cryptable/raspberry-sx/docs/images/IMG_2757.jpg

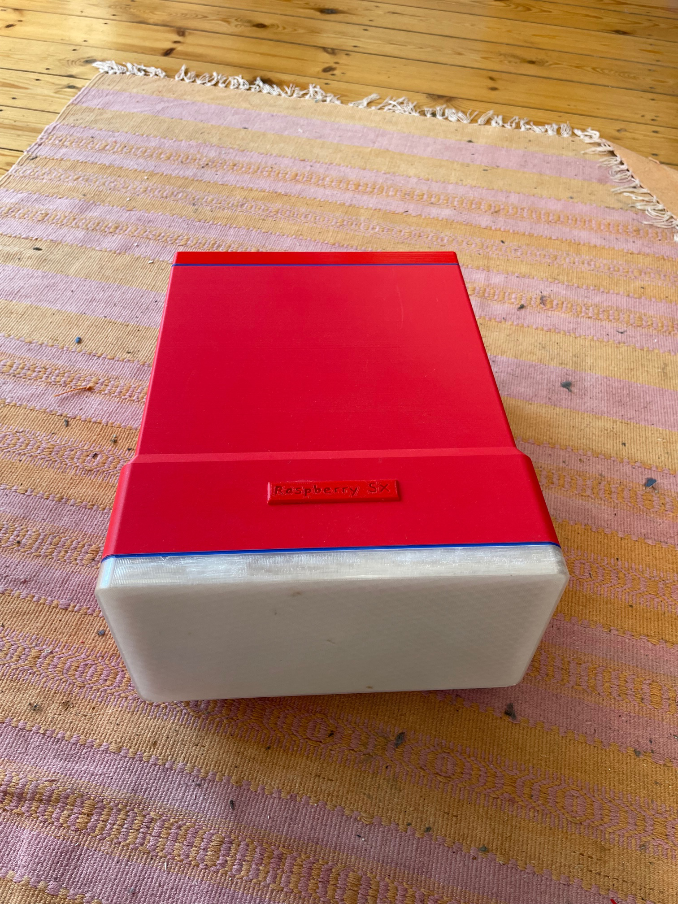
docs/images/IMG_2757.jpg
