cryptable/raspberry-sx/docs/images/IMG_2758.jpg

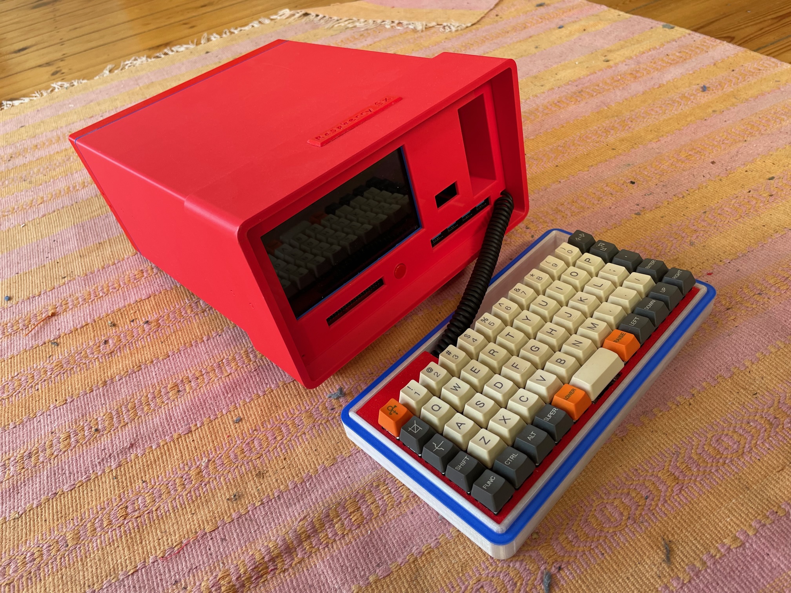
docs/images/IMG_2758.jpg
