cryptable/raspberry-sx/docs/images/IMG_2759.jpg

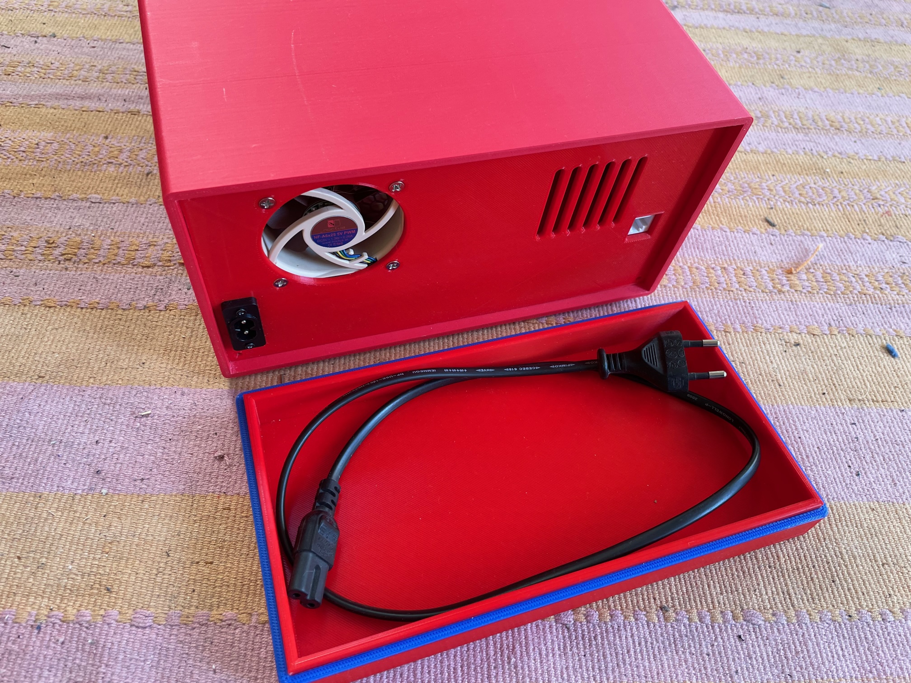
docs/images/IMG_2759.jpg
