cryptable/raspberry-sx/docs/images/IMG_2761.jpg

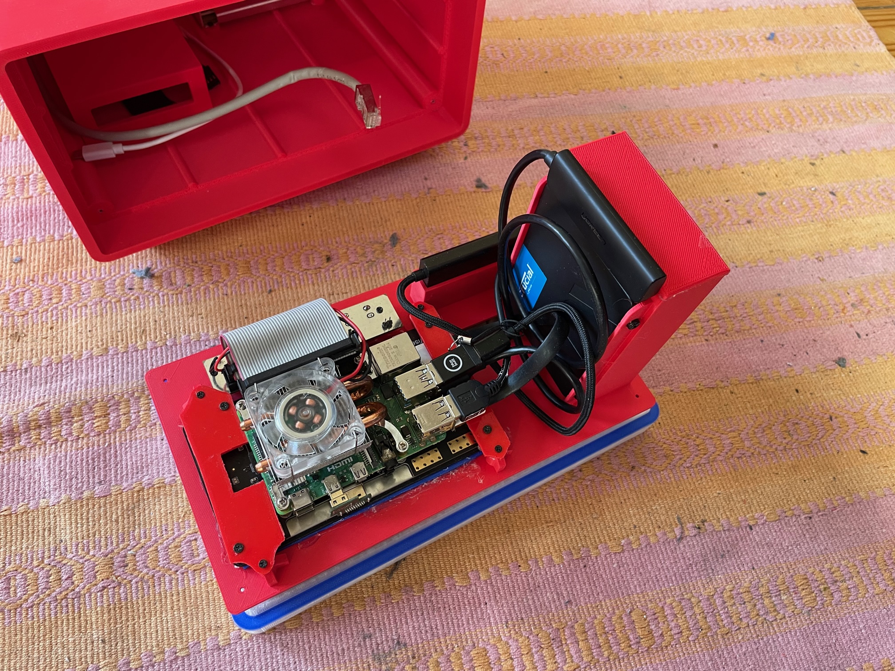
docs/images/IMG_2761.jpg
