cryptable/raspberry-sx/docs/images/IMG_2762.jpg

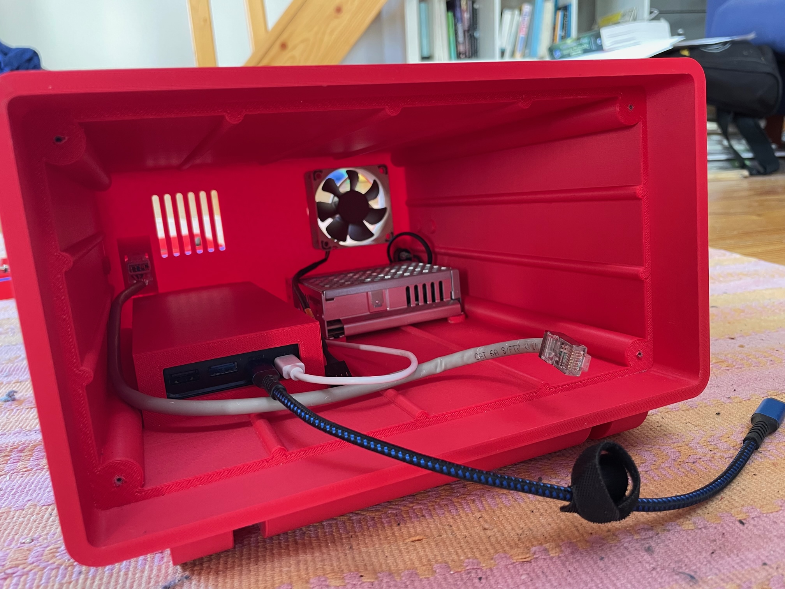
docs/images/IMG_2762.jpg
