cryptable/raspberry-sx/powercheck/cherry.h

/* GIMP RGB C-Source image dump (cherry-svgrepo-com.c) */

static const struct {
  uint  	 width;
  uint  	 height;
  uint  	 bytes_per_pixel; /* 2:RGB16, 3:RGB, 4:RGBA */ 
  uint8_t 	 pixel_data[64 * 64 * 3 + 1];
} gimp_image = {
  64, 64, 3,
  "\000\000\000\000\000\000\000\000\000\000\000\000\000\000\000\000\000\000\000\000\000\000\000\000\000\000\000\000\000\000\000\000\000\000\000\000"
  "\000\000\000\000\000\000\000\000\000\000\000\000\000\000\000\000\000\000\000\000\000\000\000\000\000\000\000\000\000\000\000\000\000\000\000\000"
  "\000\000\000\000\000\000\000\000\000\000\000\000\000\000\000\000\000\000\000\000\000\000\000\000\000\000\000\000\000\000\000\000\000\000\000\000"
  "\000\000\000\000\000\000\000\000\000\000\000\000\007\023\010\034J!\"](\036S$\010\025\011\000\000\000\000\000\000\000\000\000"
  "\000\000\000\000\000\000\000\000\000\000\000\000\000\000\000\000\000\000\000\000\000\000\000\000\000\000\000\000\000\000\000\000\000\000\000\000"
  "\000\000\000\000\000\000\000\000\000\000\000\000\000\000\000\000\000\000\000\000\000\000\000\000\000\000\000\000\000\000\000\000\000\000\000\000"
  "\000\000\000\000\000\000\000\000\000\000\000\000\000\000\000\000\000\000\000\000\000\000\000\000\000\000\000\000\000\000\000\000\000\000\000\000"
  "\000\000\000\000\000\000\000\000\000\000\000\000\000\000\000\000\000\000\000\000\000\000\000\000\000\000\000\000\000\000\000\000\000\000\000\000"
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
  "@A\340CD\312==\230..L\027\027\005\002\002\000\000\000\000\000\000\000\000\000\000\000\000\000\000\000\000\000\000\000\000"
  "\000\000\000\000\000\000\000\000\000\000\000\000\000\000\000\000\000\000\000\000\000\000\000\000\000",
};
